nishibra/ROBO-ONE_Beginners_auto/pics_git/joint_base_A.png

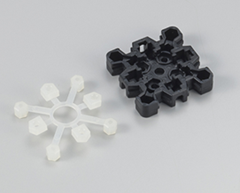
pics_git/joint_base_A.png
