nishibra/ROBO-ONE_Beginners_auto/pics_git/pb_sw_h.png

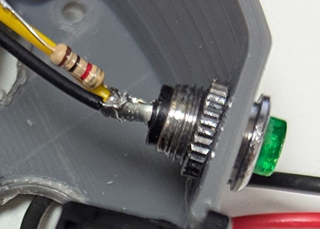
pics_git/pb_sw_h.png
